ryomuk/Teensy-4001/hardware/rev0.1/TeensyMCS4Memory/TeensyMCS4Memory.kicad_sch

## KiCad design hardware/rev0.1/TeensyMCS4Memory/TeensyMCS4Memory.kicad_sch (2023-05-09)

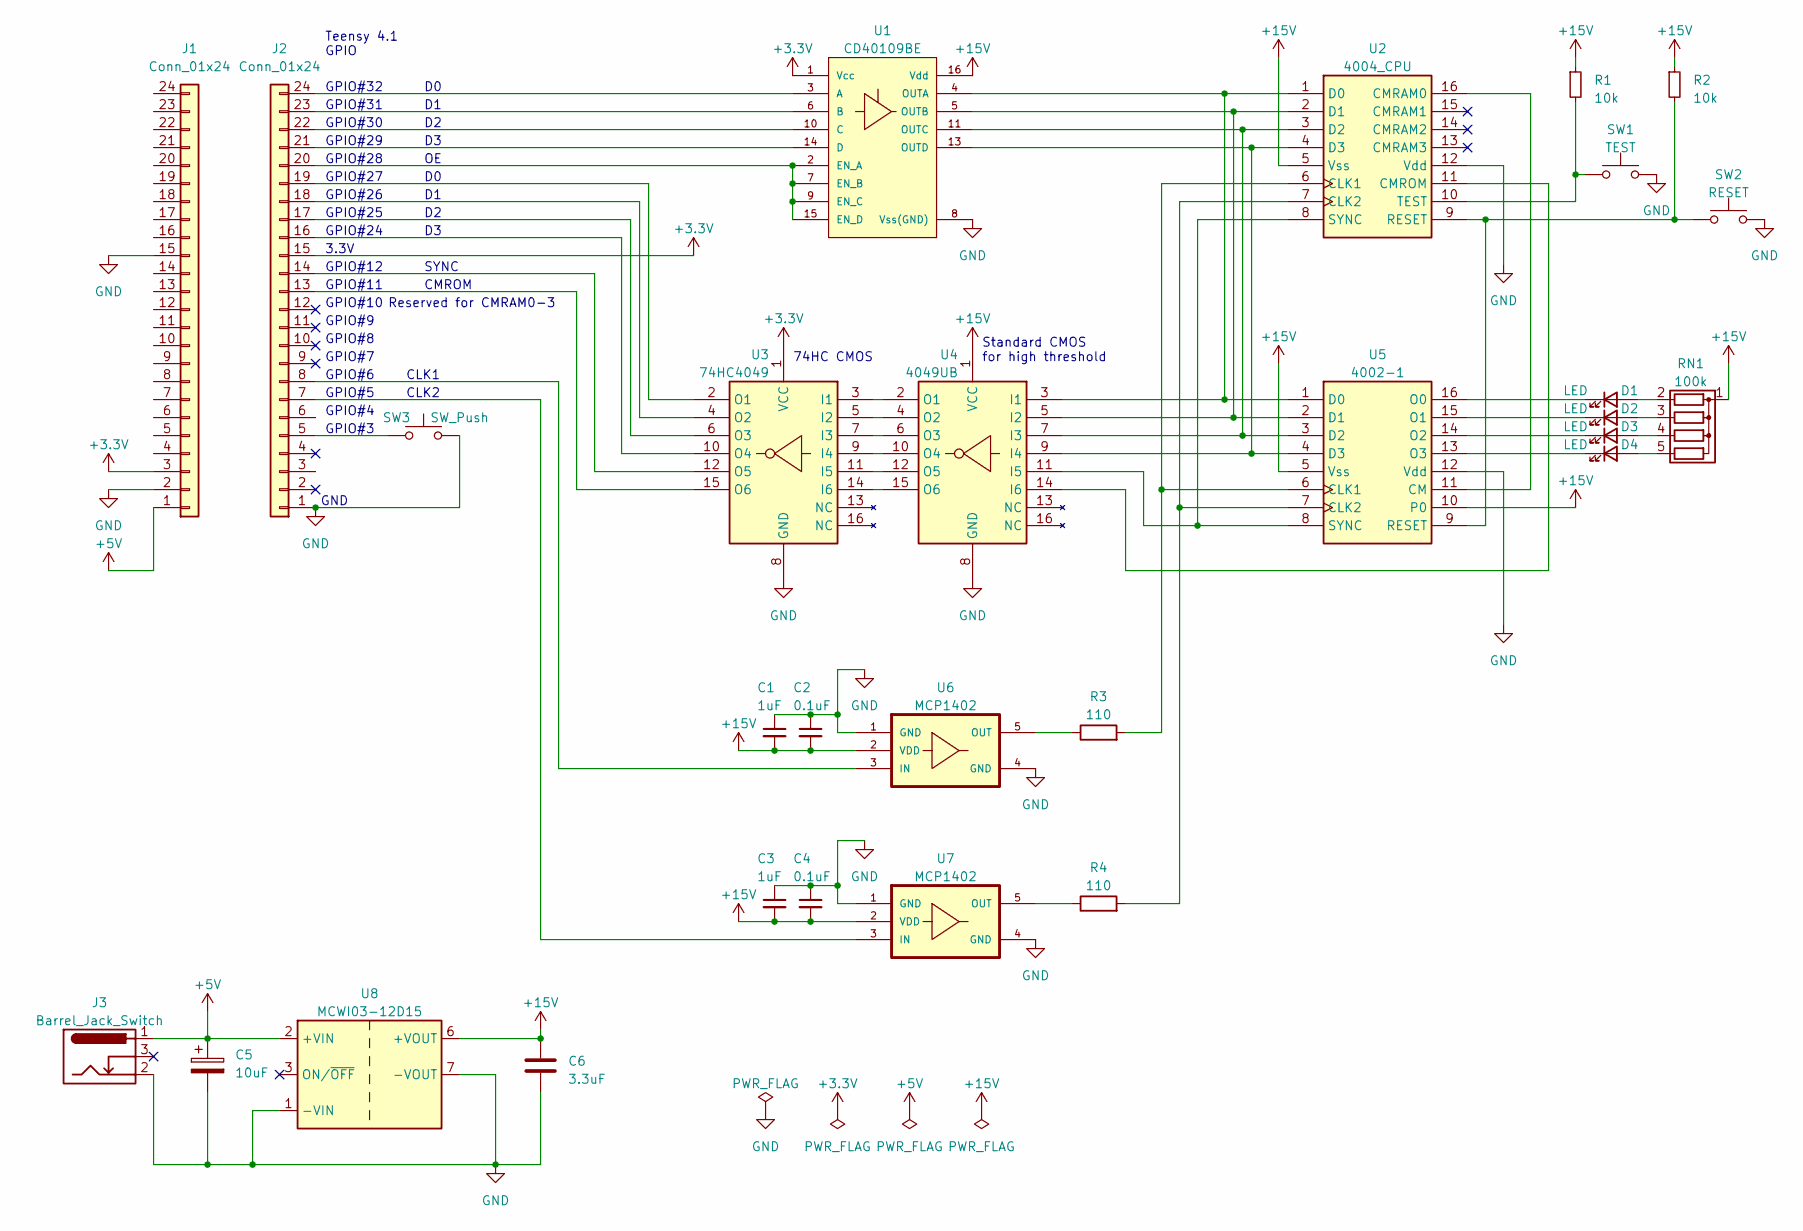
[picture p3: schematic TeensyMCS4Memory.kicad_sch]

Parts:
C1, C3: 1uF
C2, C4: 0.1uF
C5: 10uF
C6: 3.3uF
D1, D2, D3, D4: LED
J1, J2: Conn_01x24
J3: Barrel_Jack_Switch
R1, R2: 10k
R3, R4: 110
RN1: 100k; R_Array_SIP5
SW1: TEST
SW2: RESET
SW3: SW_Push
U1: CD40109BE; DIP794W45P254L1969H508Q16
U2: 4004_CPU
U3: 74HC4049
U4: 4049UB
U5: 4002-1
U6, U7: MCP1402; SOT95P270X145-5N
U8: MCWI03-12D15

Connections:
+3.3V: J1.3, J2.15, U1.1 (Vcc), U3.1 (VCC)
+5V: C5.1, J1.1, J3.1, U8.2 (+VIN)
+15V: C1.2, C2.2, C3.2, C4.2, C6.1, R1.1, R2.1, RN1.1 (common), U1.16 (Vdd), U2.5 (Vss), U4.1 (VCC), U5.5 (Vss), U5.10 (P0), U6.2 (VDD), U7.2 (VDD), U8.6 (+VOUT)
GND: C1.1, C2.1, C3.1, C4.1, C5.2, C6.2, J1.2, J1.15, J2.1, J3.2, SW1.2, SW2.2, SW3.2, U1.8 (Vss(GND)), U2.12 (Vdd), U3.8 (GND), U4.8 (GND), U5.12 (Vdd), U6.1 (GND), U6.4 (GND), U7.1 (GND), U7.4 (GND), U8.1 (-VIN), U8.7 (-VOUT)
unnamed: D1.1 (K), U5.16 (O0)
unnamed: D1.2 (A), RN1.2 (R1)
unnamed: D2.1 (K), U5.15 (O1)
unnamed: D2.2 (A), RN1.3 (R2)
unnamed: D3.1 (K), U5.14 (O2)
unnamed: D3.2 (A), RN1.4 (R3)
unnamed: D4.1 (K), U5.13 (O3)
unnamed: D4.2 (A), RN1.5 (R4)
unnamed: J2.5, SW3.1
unnamed: J2.7, U7.3 (IN)
unnamed: J2.8, U6.3 (IN)
unnamed: J2.13, U3.15 (O6)
unnamed: J2.14, U3.12 (O5)
unnamed: J2.16, U3.10 (O4)
unnamed: J2.17, U3.6 (O3)
unnamed: J2.18, U3.4 (O2)
unnamed: J2.19, U3.2 (O1)
unnamed: J2.20, U1.2 (EN_A), U1.7 (EN_B), U1.9 (EN_C), U1.15 (EN_D)
unnamed: J2.21, U1.14 (D)
unnamed: J2.22, U1.10 (C)
unnamed: J2.23, U1.6 (B)
unnamed: J2.24, U1.3 (A)
unnamed: R1.2, SW1.1, U2.10 (TEST)
unnamed: R2.2, SW2.1, U2.9 (RESET), U5.9 (RESET)
unnamed: R3.1, U6.5 (OUT)
unnamed: R3.2, U2.6 (CLK1), U5.6 (CLK1)
unnamed: R4.1, U7.5 (OUT)
unnamed: R4.2, U2.7 (CLK2), U5.7 (CLK2)
unnamed: U1.4 (OUTA), U2.1 (D0), U4.3 (I1), U5.1 (D0)
unnamed: U1.5 (OUTB), U2.2 (D1), U4.5 (I2), U5.2 (D1)
unnamed: U1.11 (OUTC), U2.3 (D2), U4.7 (I3), U5.3 (D2)
unnamed: U1.13 (OUTD), U2.4 (D3), U4.9 (I4), U5.4 (D3)
unnamed: U2.8 (SYNC), U4.11 (I5), U5.8 (SYNC)
unnamed: U2.11 (CMROM), U4.14 (I6)
unnamed: U2.16 (CMRAM0), U5.11 (CM)
unnamed: U3.3 (I1), U4.2 (O1)
unnamed: U3.5 (I2), U4.4 (O2)
unnamed: U3.7 (I3), U4.6 (O3)
unnamed: U3.9 (I4), U4.10 (O4)
unnamed: U3.11 (I5), U4.12 (O5)
unnamed: U3.14 (I6), U4.15 (O6)

Notes on the sheet:
GPIO#31
GPIO#6
Standard CMOS for high threshold
GPIO#26
74HC CMOS
GPIO#3
GPIO#25
GPIO#10
CMROM
GPIO#28
GPIO#27
Teensy 4.1 GPIO
GPIO#12
CLK2
Reserved for CMRAM0-3
GPIO#32
GPIO#5
GPIO#7
SYNC
GPIO#8
GPIO#4
CLK1
3.3V
GND
GPIO#9
GPIO#30
GPIO#24
GPIO#11
GPIO#29
